ploopyco/nano-2-trackball/docs/img/4.jpg

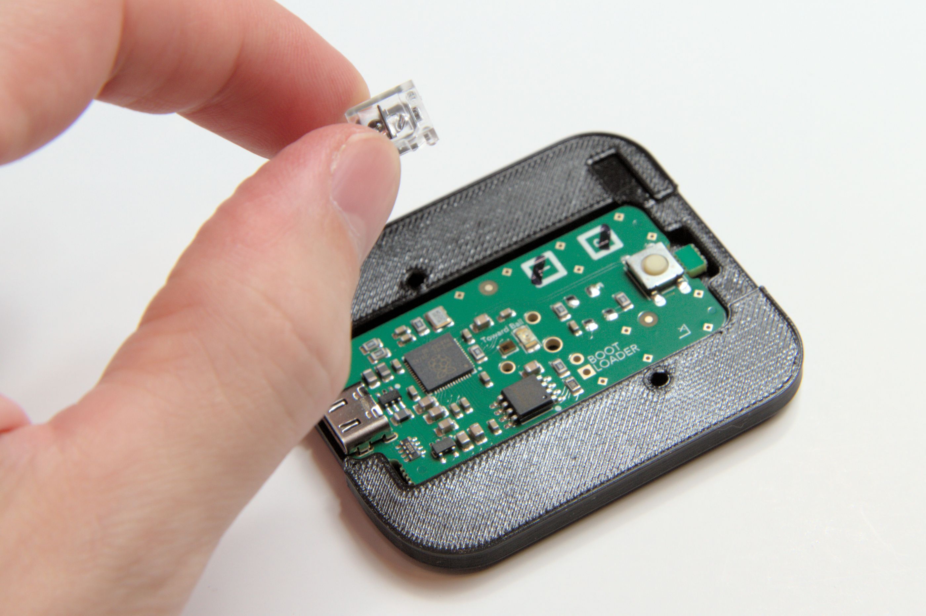
docs/img/4.jpg
